TongSUE/TECHIN-514-Project/custom PCB/schematic screenshots.png

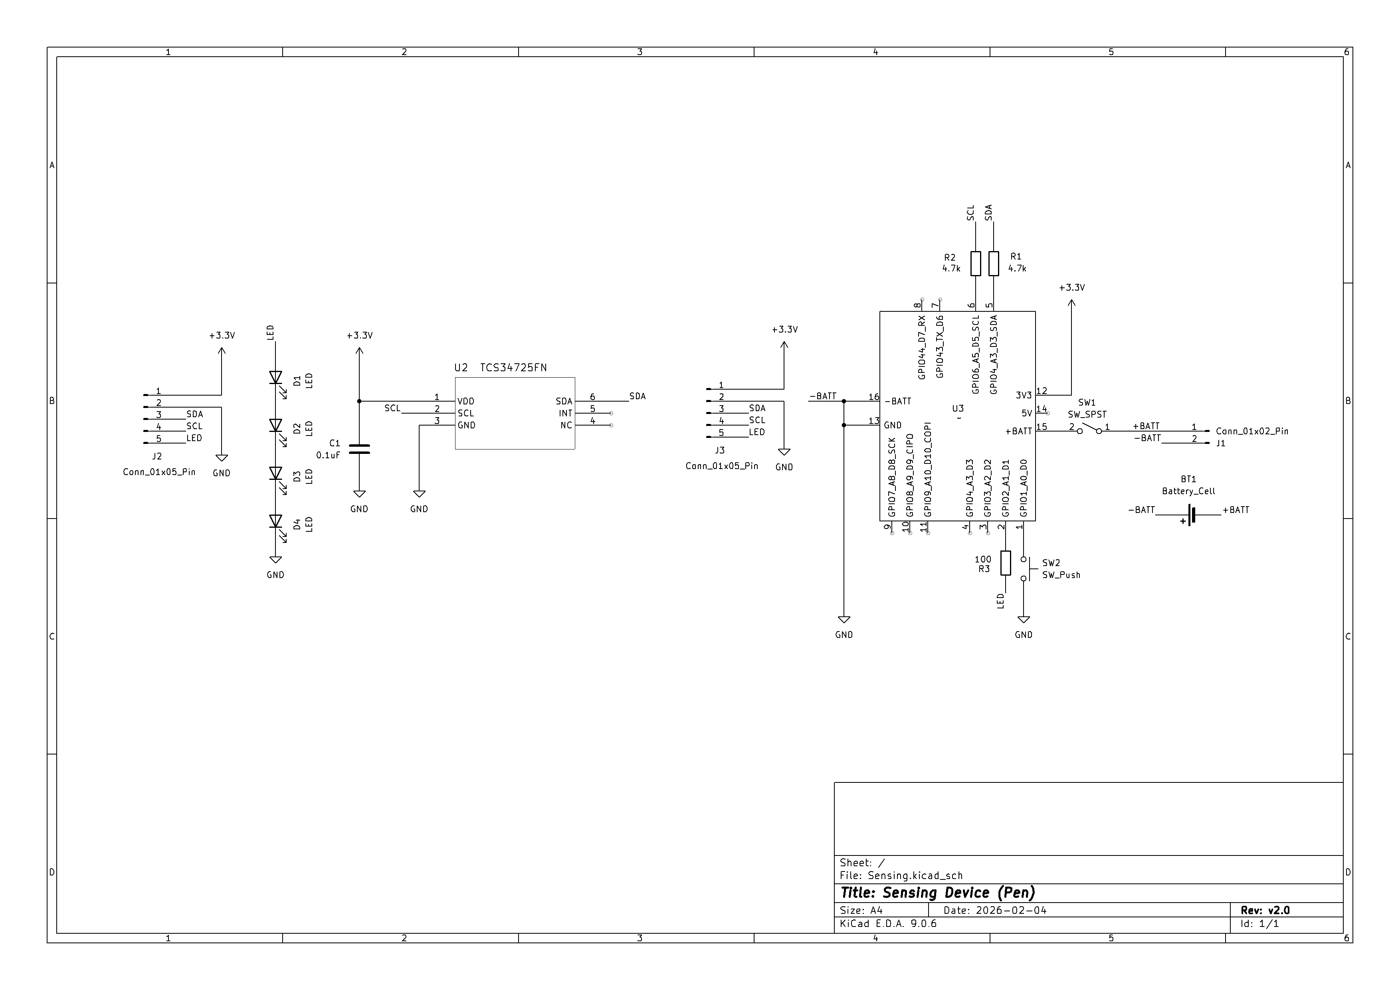
custom PCB/schematic screenshots.png
