TongSUE/TECHIN-514-Project/enclosure/display_enclosure_3.png

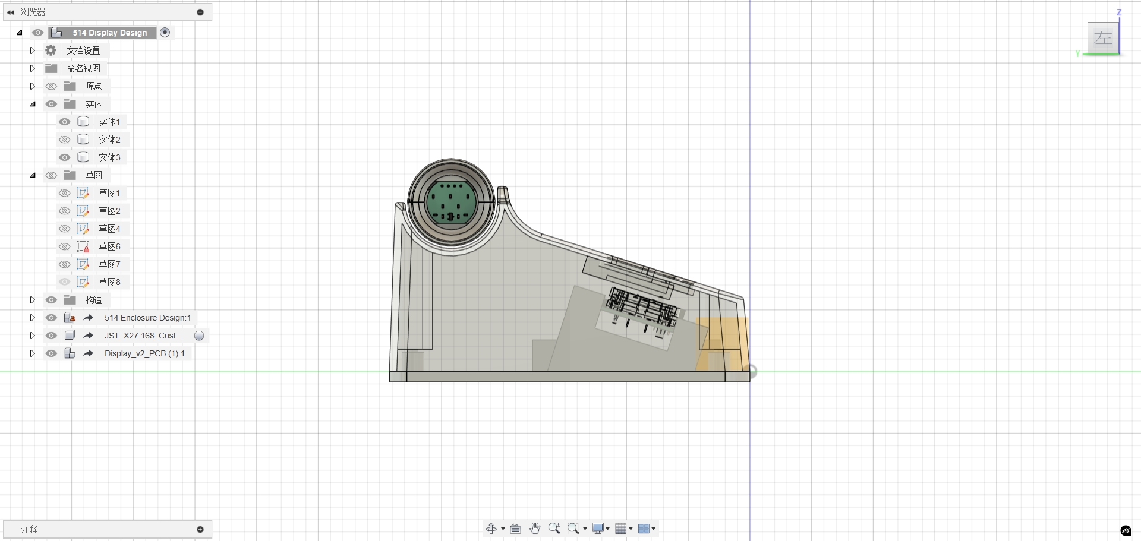
enclosure/display_enclosure_3.png
