TongSUE/TECHIN-514-Project/enclosure/display_enclosure_4.png

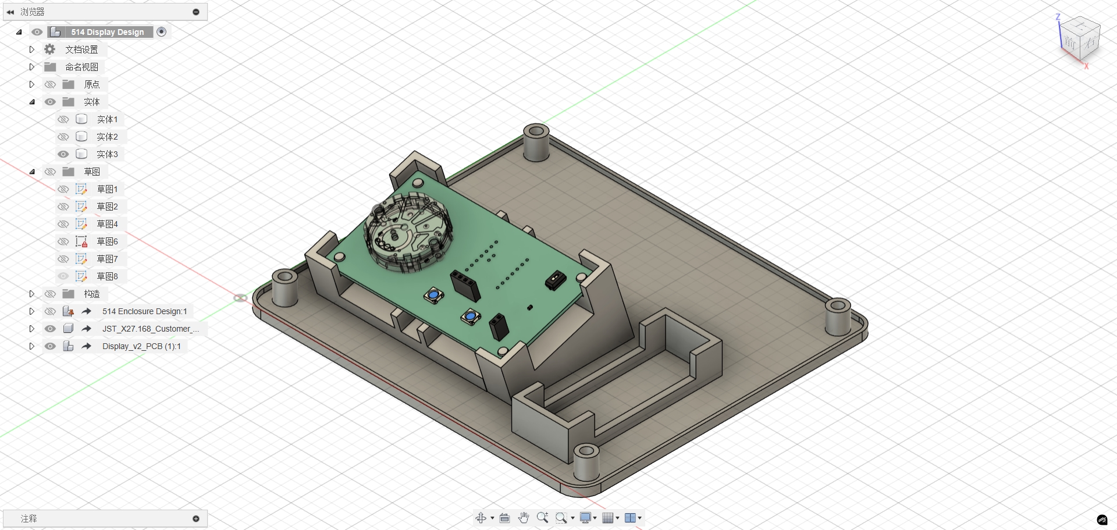
enclosure/display_enclosure_4.png
