TongSUE/TECHIN-514-Project/images/sensor_main_board_pcb.png

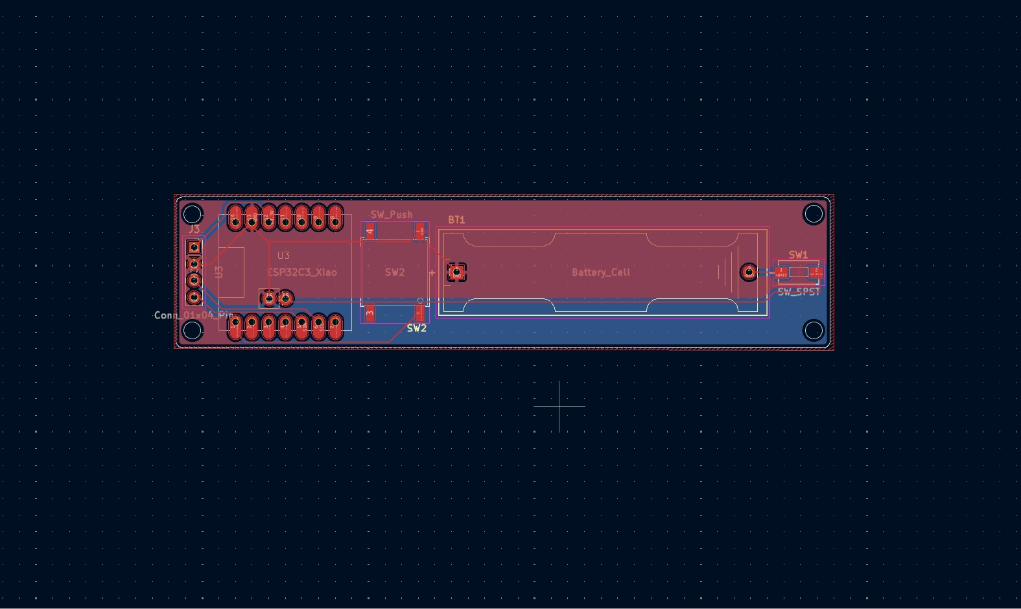
images/sensor_main_board_pcb.png
