TongSUE/TECHIN-514-Project/images/sensor_main_board_pcb_v2.png

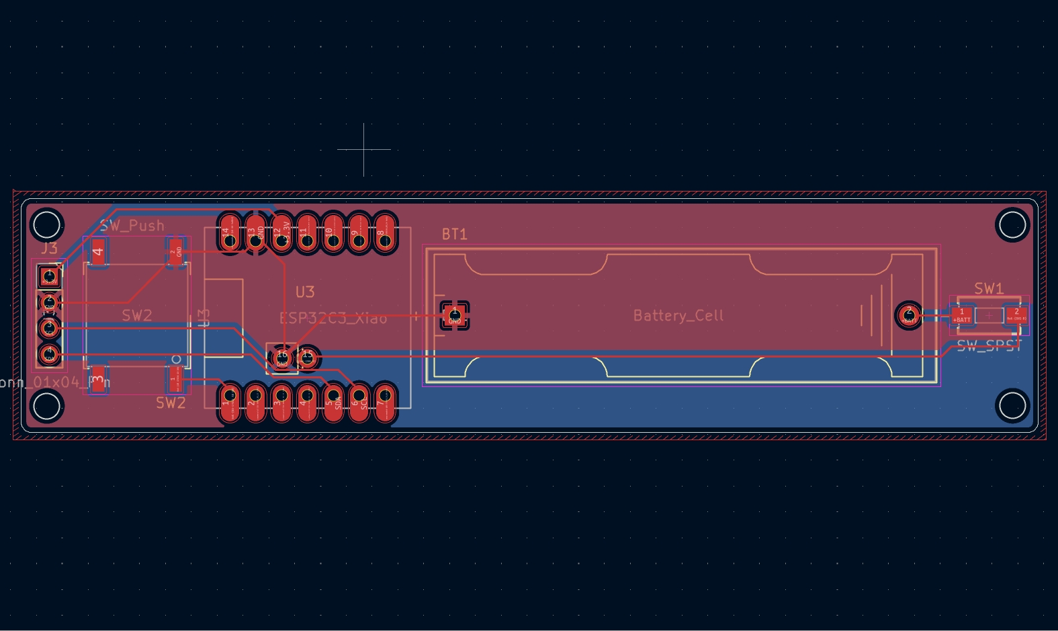
images/sensor_main_board_pcb_v2.png
