TongSUE/TECHIN-514-Project/images/sensor_tip_pcb.png

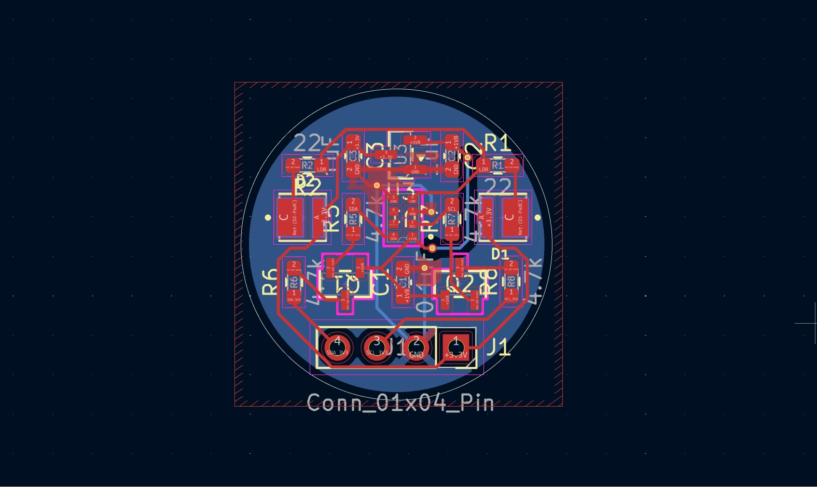
images/sensor_tip_pcb.png
