TongSUE/TECHIN-514-Project/images/sensor_tip_pcb_v2.png

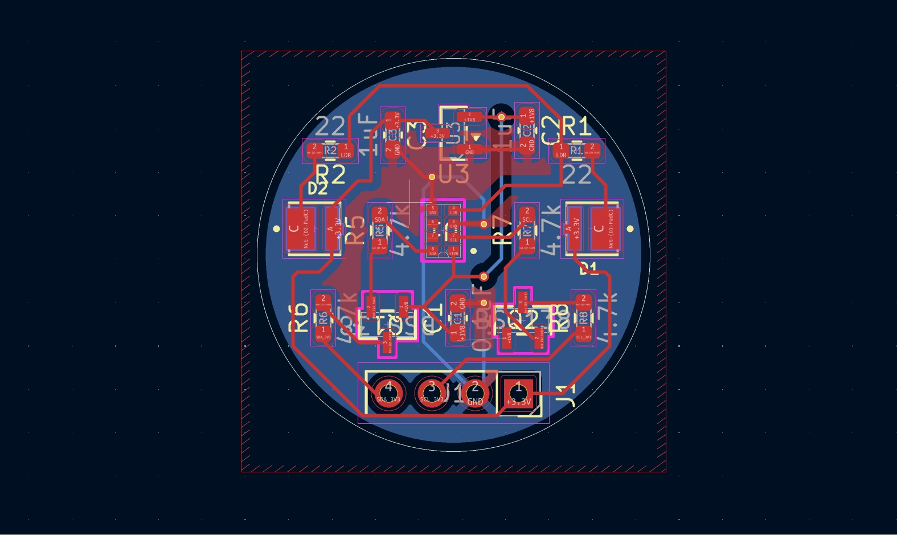
images/sensor_tip_pcb_v2.png
